PeterJensen/nascom-esp/src/NascomFont.h

#include <stdint.h>

const uint8_t nascomFontPixels[16*256] = {
    0x7F, 0x41, 0x41, 0x41, 0x41, 0x41, 0x41, 0x41,
    0x7F, 0x00, 0x00, 0x00, 0x00, 0x00, 0x00, 0x00,
    0x7F, 0x40, 0x40, 0x40, 0x40, 0x40, 0x40, 0x40,
    0x40, 0x00, 0x00, 0x00, 0x00, 0x00, 0x00, 0x00,
    0x08, 0x08, 0x08, 0x08, 0x08, 0x08, 0x08, 0x08,
    0x7F, 0x00, 0x00, 0x00, 0x00, 0x00, 0x00, 0x00,
    0x01, 0x01, 0x01, 0x01, 0x01, 0x01, 0x01, 0x01,
    0x7F, 0x00, 0x00, 0x00, 0x00, 0x00, 0x00, 0x00,
    0x20, 0x10, 0x08, 0x04, 0x3E, 0x10, 0x08, 0x04,
    0x02, 0x00, 0x00, 0x00, 0x00, 0x00, 0x00, 0x00,
    0x7F, 0x41, 0x63, 0x55, 0x49, 0x55, 0x63, 0x41,
    0x7F, 0x00, 0x00, 0x00, 0x00, 0x00, 0x00, 0x00,
    0x00, 0x01, 0x02, 0x04, 0x48, 0x50, 0x60, 0x40,
    0x00, 0x00, 0x00, 0x00, 0x00, 0x00, 0x00, 0x00,
    0x1C, 0x22, 0x41, 0x41, 0x41, 0x7F, 0x14, 0x14,
    0x77, 0x00, 0x00, 0x00, 0x00, 0x00, 0x00, 0x00,
    0x10, 0x20, 0x7C, 0x22, 0x11, 0x01, 0x01, 0x01,
    0x01, 0x00, 0x00, 0x00, 0x00, 0x00, 0x00, 0x00,
    0x00, 0x08, 0x04, 0x02, 0x7F, 0x02, 0x04, 0x08,
    0x00, 0x00, 0x00, 0x00, 0x00, 0x00, 0x00, 0x00,
    0x7F, 0x00, 0x00, 0x00, 0x7F, 0x00, 0x00, 0x00,
    0x7F, 0x00, 0x00, 0x00, 0x00, 0x00, 0x00, 0x00,
    0x00, 0x08, 0x08, 0x08, 0x49, 0x2A, 0x1C, 0x08,
    0x00, 0x00, 0x00, 0x00, 0x00, 0x00, 0x00, 0x00,
    0x08, 0x08, 0x2A, 0x1C, 0x08, 0x49, 0x2A, 0x1C,
    0x08, 0x00, 0x00, 0x00, 0x00, 0x00, 0x00, 0x00,
    0x00, 0x08, 0x10, 0x20, 0x7F, 0x20, 0x10, 0x08,
    0x00, 0x00, 0x00, 0x00, 0x00, 0x00, 0x00, 0x00,
    0x1C, 0x22, 0x63, 0x55, 0x49, 0x55, 0x63, 0x22,
    0x1C, 0x00, 0x00, 0x00, 0x00, 0x00, 0x00, 0x00,
    0x1C, 0x22, 0x41, 0x41, 0x49, 0x41, 0x41, 0x22,
    0x1C, 0x00, 0x00, 0x00, 0x00, 0x00, 0x00, 0x00,
    0x7F, 0x41, 0x41, 0x41, 0x7F, 0x41, 0x41, 0x41,
    0x7F, 0x00, 0x00, 0x00, 0x00, 0x00, 0x00, 0x00,
    0x1C, 0x2A, 0x49, 0x49, 0x4F, 0x41, 0x41, 0x22,
    0x1C, 0x00, 0x00, 0x00, 0x00, 0x00, 0x00, 0x00,
    0x1C, 0x22, 0x41, 0x41, 0x4F, 0x49, 0x49, 0x2A,
    0x1C, 0x00, 0x00, 0x00, 0x00, 0x00, 0x00, 0x00,
    0x1C, 0x22, 0x41, 0x41, 0x79, 0x49, 0x49, 0x2A,
    0x1C, 0x00, 0x00, 0x00, 0x00, 0x00, 0x00, 0x00,
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
};

Font NascomFont(8, 16, nascomFontPixels, 0, 256, true);
